thecowgoesmoo/TwinCl/CNC/files/octave_naturals_v2.png

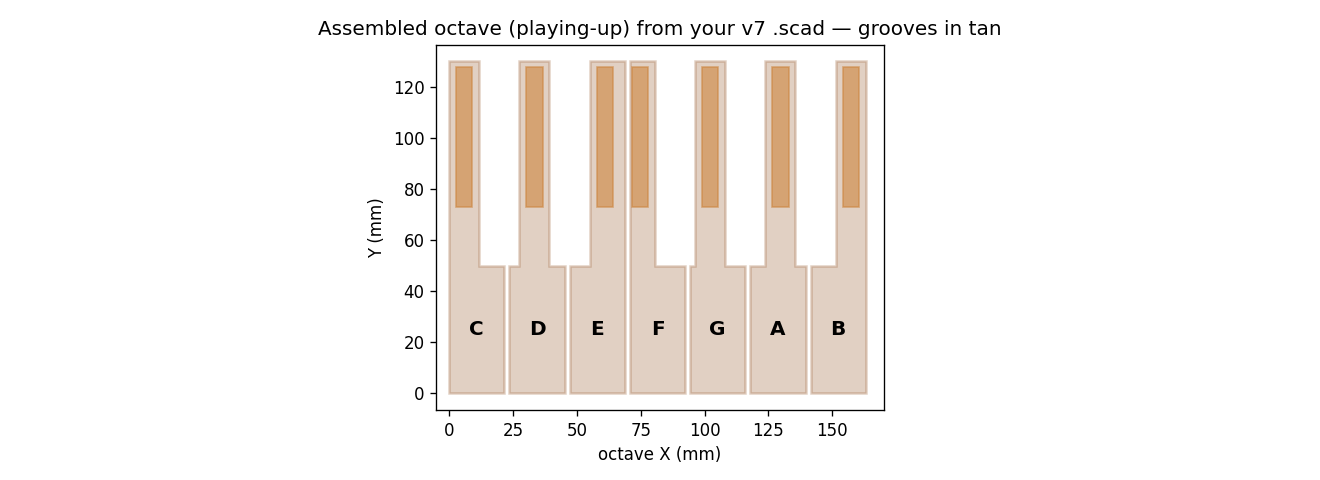
CNC/files/octave_naturals_v2.png
