thecowgoesmoo/TwinCl/model_sim/FirstPulse_simRigidExc.png

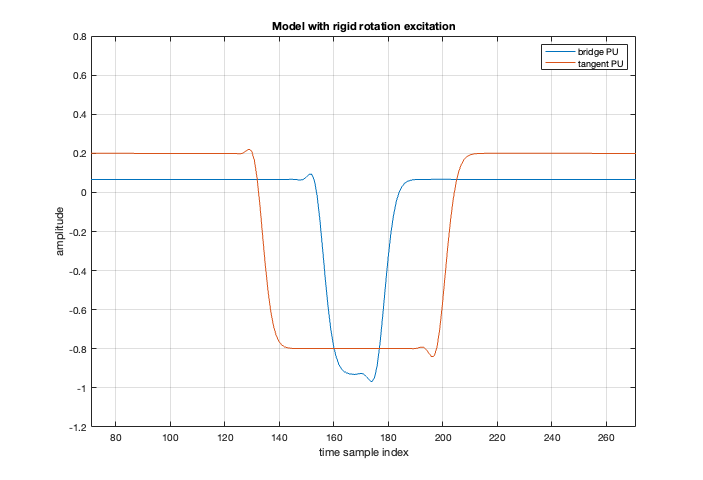
model_sim/FirstPulse_simRigidExc.png
