thecowgoesmoo/TwinCl/model_sim/FirstPulse_TC002meas.png

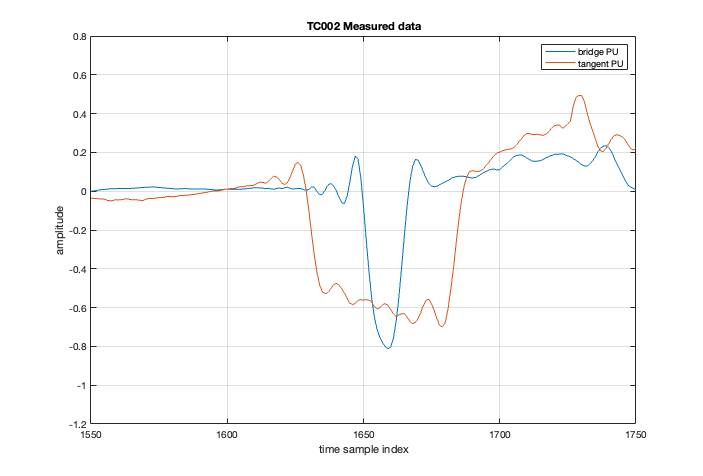
model_sim/FirstPulse_TC002meas.png
