thecowgoesmoo/TwinCl/model_sim/fitHCTparams_demo_hct.png

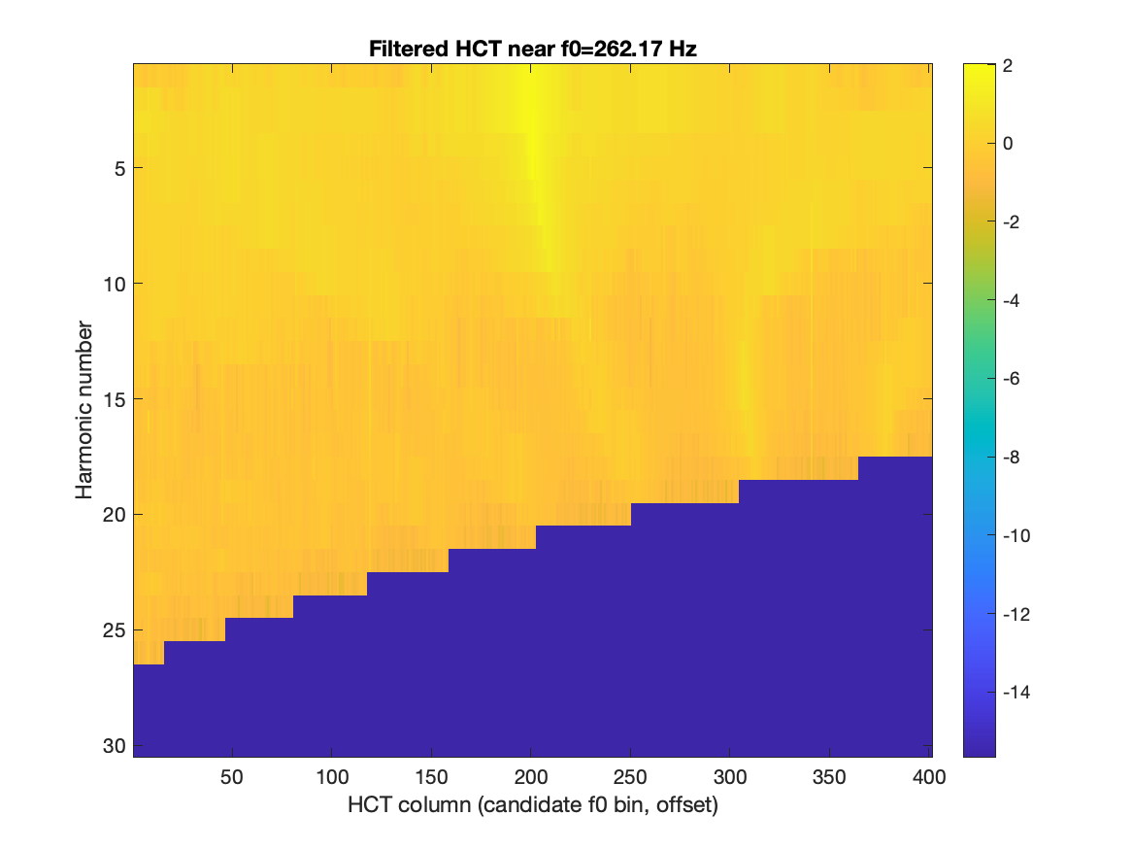
model_sim/fitHCTparams_demo_hct.png
