thecowgoesmoo/TwinCl/model_sim/fitHCTparams_demo_profile.png

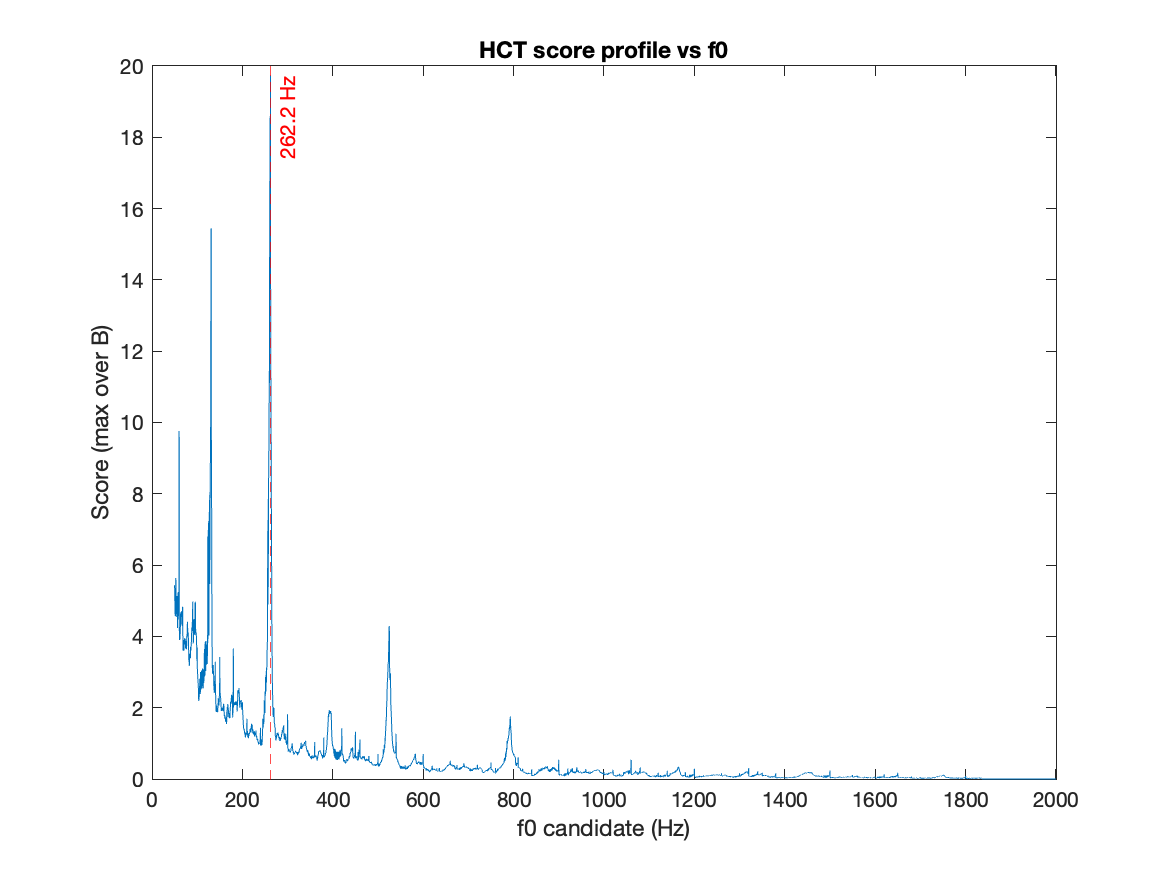
model_sim/fitHCTparams_demo_profile.png
