thecowgoesmoo/TwinCl/model_sim/fitHCTparams_demo_score.png

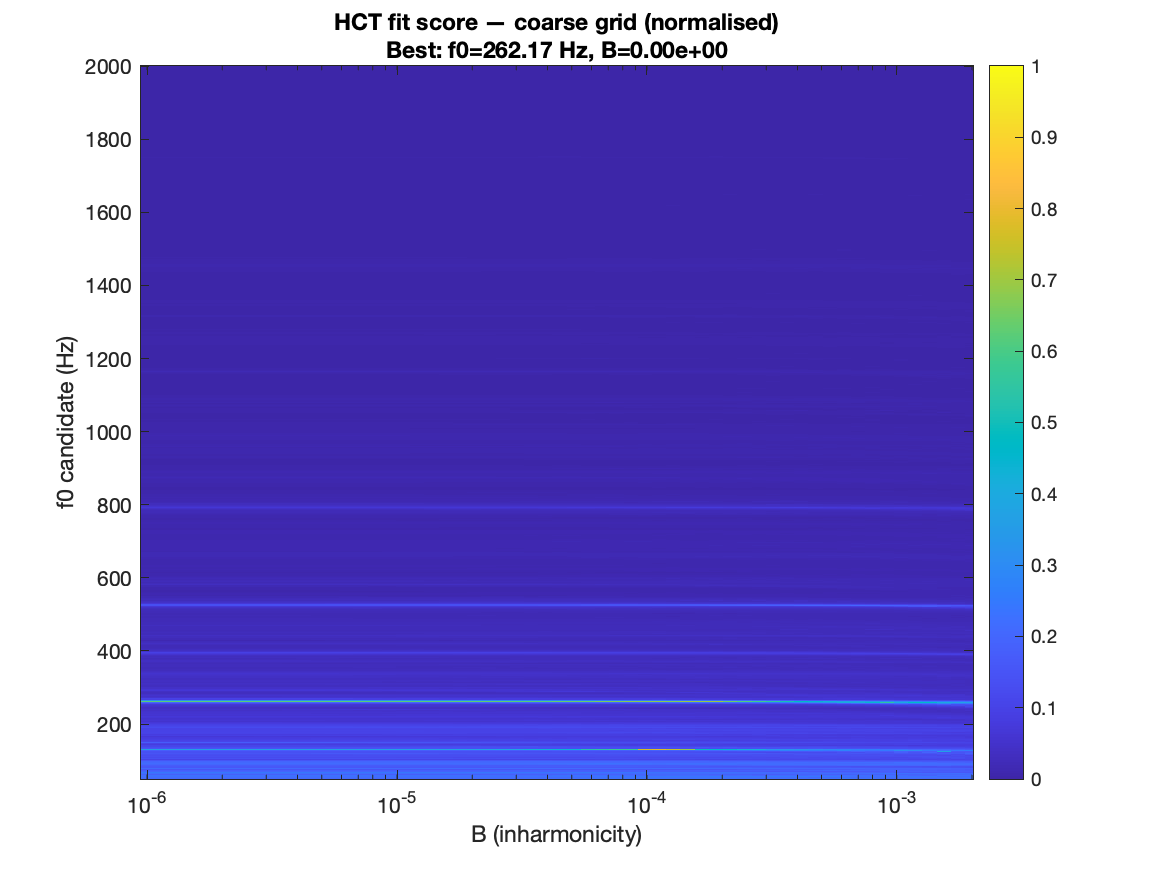
model_sim/fitHCTparams_demo_score.png
