thecowgoesmoo/TwinCl/prototypes/TC-001/media/photos/TwinCl_v1.jpeg

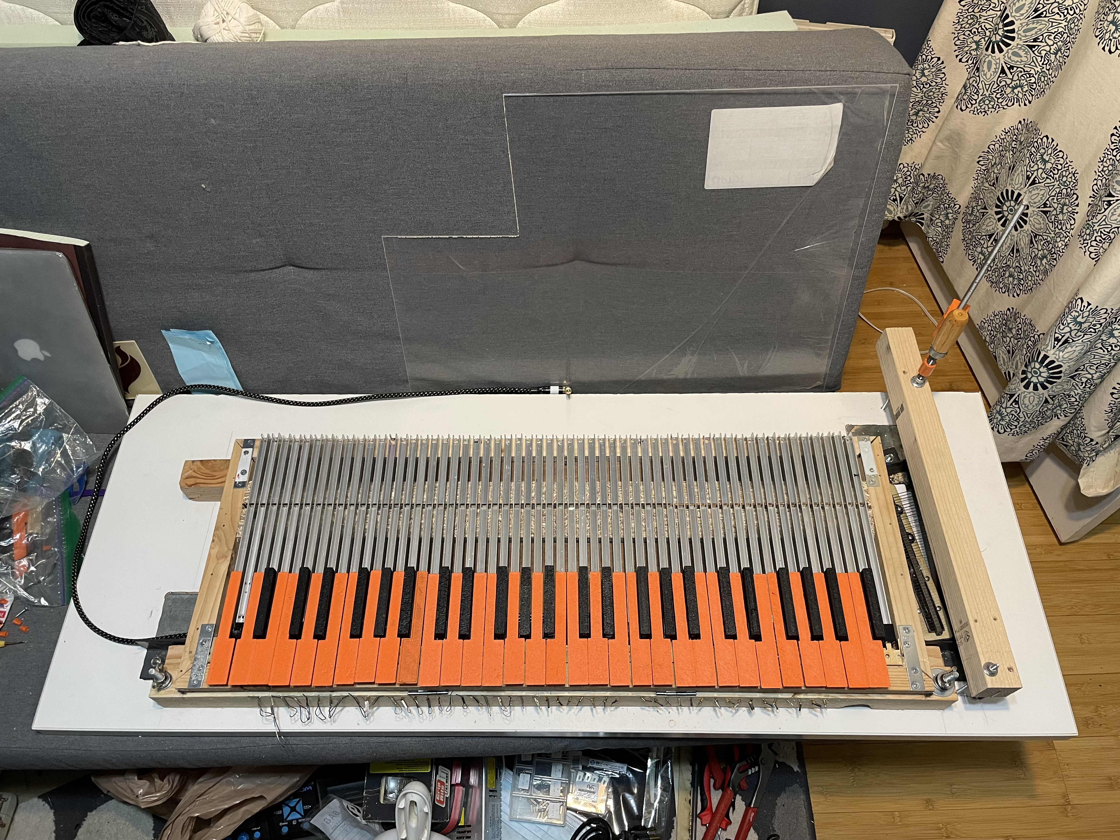
prototypes/TC-001/media/photos/TwinCl_v1.jpeg
