thecowgoesmoo/TwinCl/prototypes/TC-001/media/photos/TwinCl_v1_open.jpeg

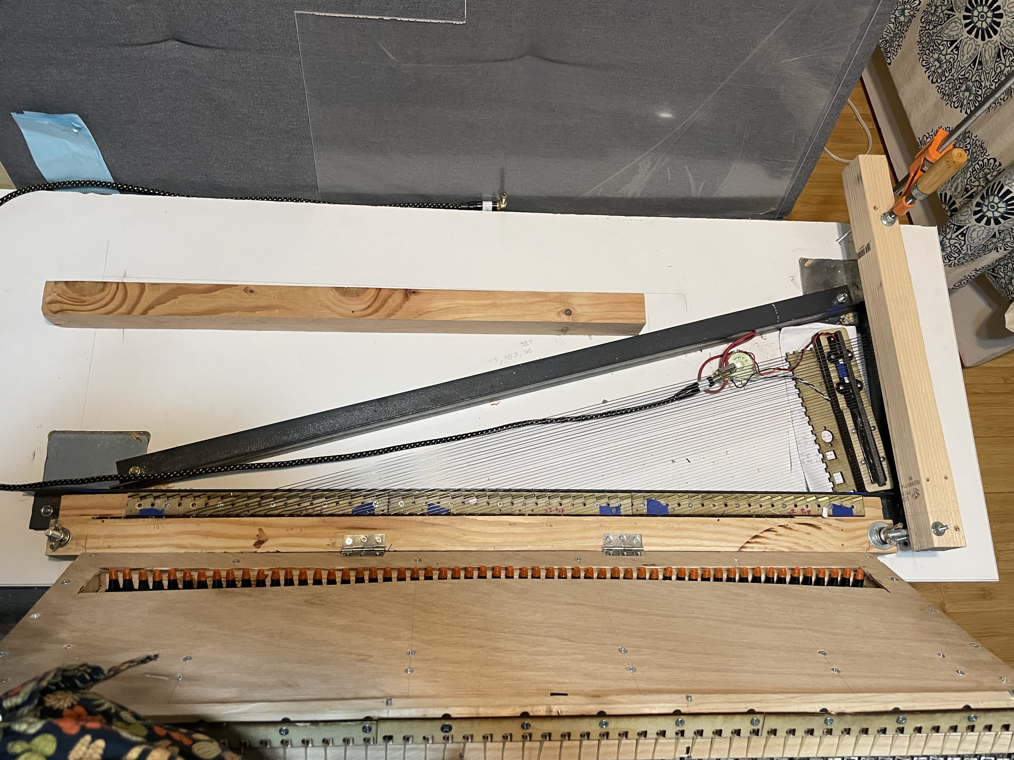
prototypes/TC-001/media/photos/TwinCl_v1_open.jpeg
