thecowgoesmoo/TwinCl/prototypes/TC-002/media/photos/HarpV2.jpeg

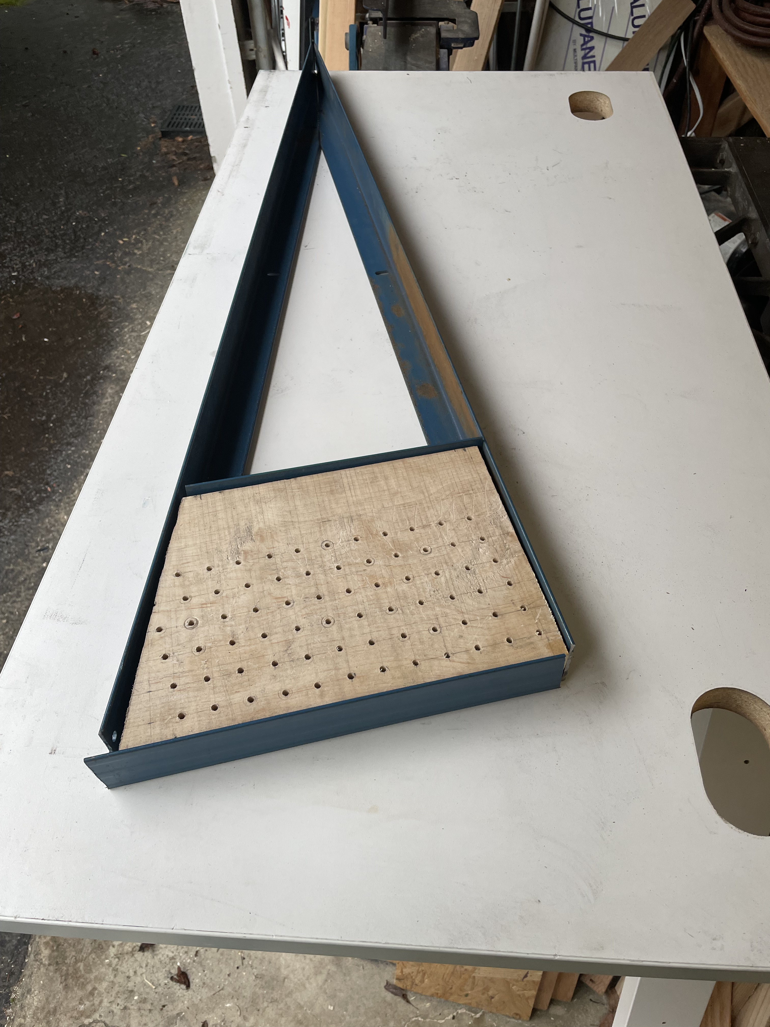
prototypes/TC-002/media/photos/HarpV2.jpeg
