thecowgoesmoo/TwinCl/prototypes/TC-002/media/photos/SupahTunah.jpeg

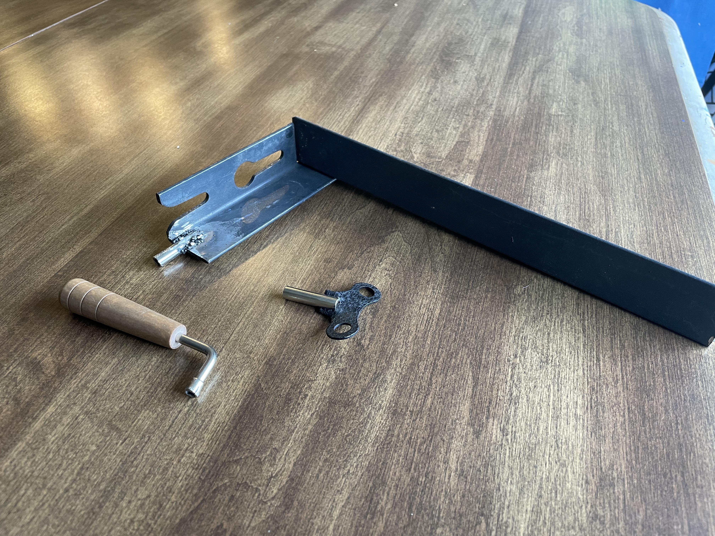
prototypes/TC-002/media/photos/SupahTunah.jpeg
