thecowgoesmoo/TwinCl/prototypes/TC-002/media/photos/TwinCl_v2_KeyworkDetail.jpeg

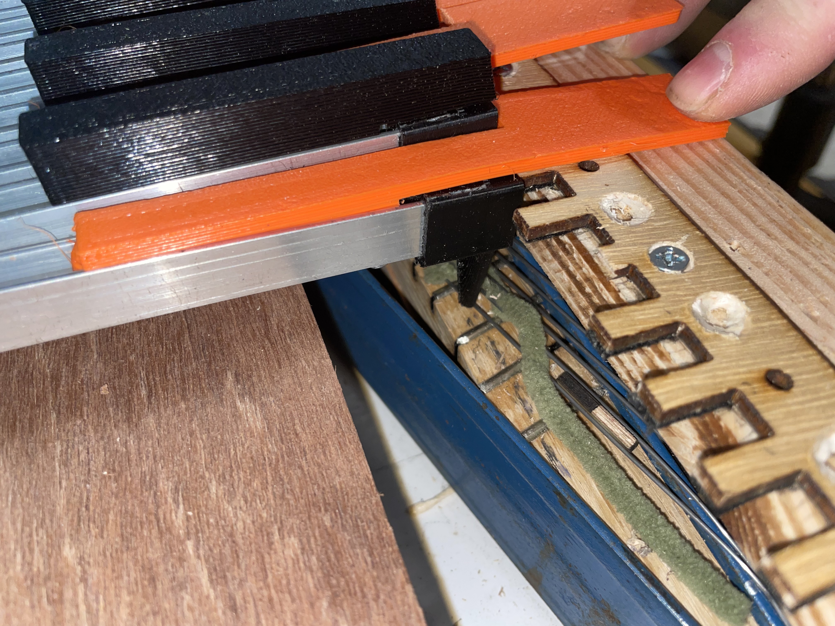
prototypes/TC-002/media/photos/TwinCl_v2_KeyworkDetail.jpeg
