thecowgoesmoo/TwinCl/prototypes/TC-003/media/photos/IMG_6832.jpeg

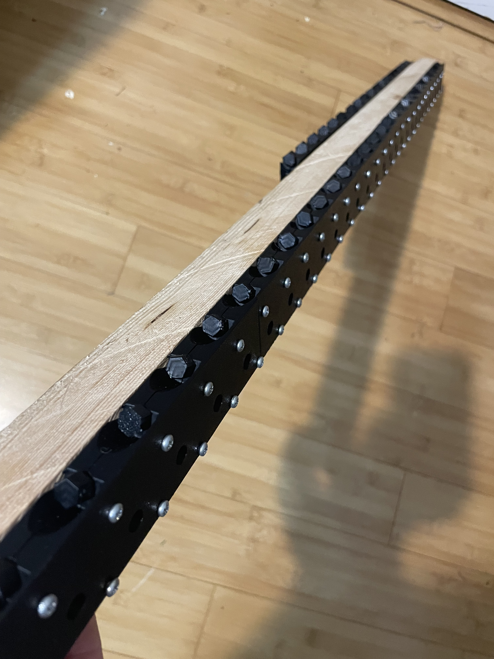
prototypes/TC-003/media/photos/IMG_6832.jpeg
