thecowgoesmoo/TwinCl/prototypes/TC-003/media/photos/IMG_6854.jpeg

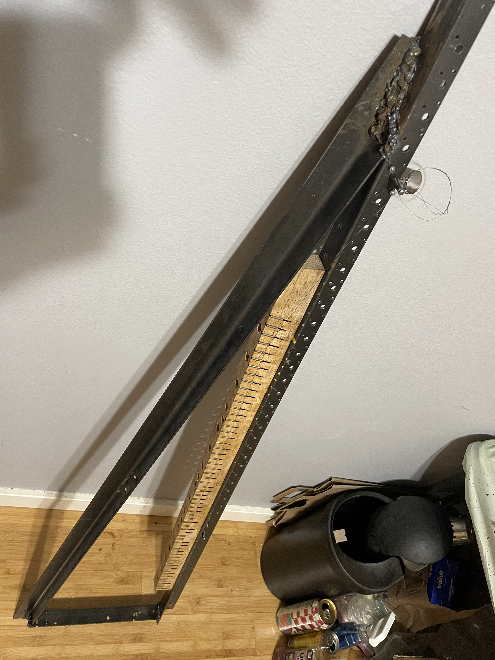
prototypes/TC-003/media/photos/IMG_6854.jpeg
