thecowgoesmoo/TwinCl/prototypes/TC-003/media/photos/IMG_6858.jpeg

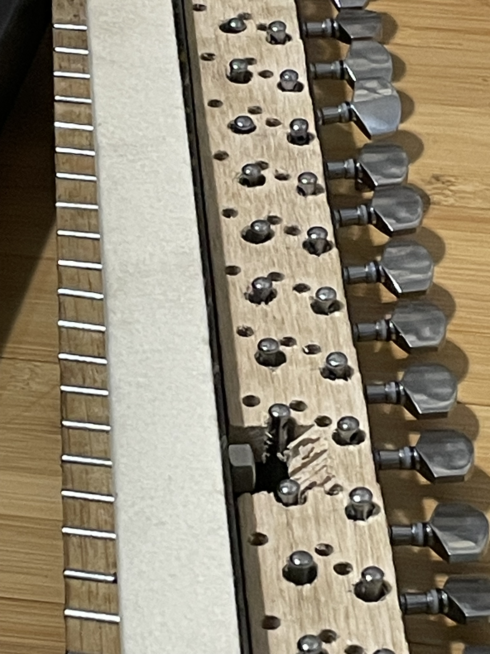
prototypes/TC-003/media/photos/IMG_6858.jpeg
