thecowgoesmoo/TwinCl/prototypes/TC-003/media/photos/IMG_6859.jpeg

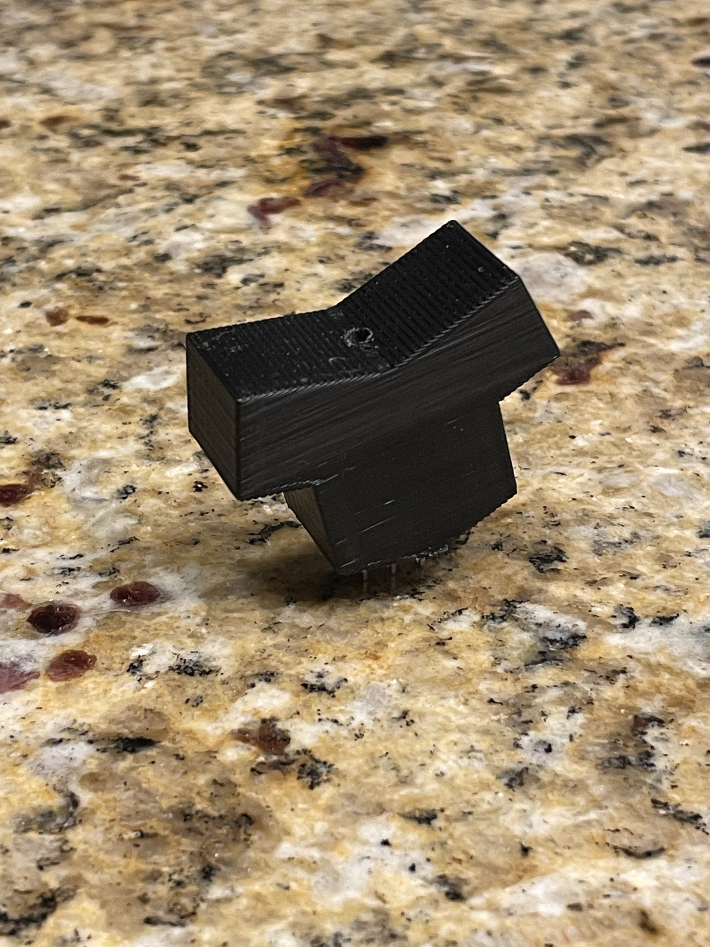
prototypes/TC-003/media/photos/IMG_6859.jpeg
