thecowgoesmoo/TwinCl/prototypes/TC-003/media/photos/IMG_6860.jpeg

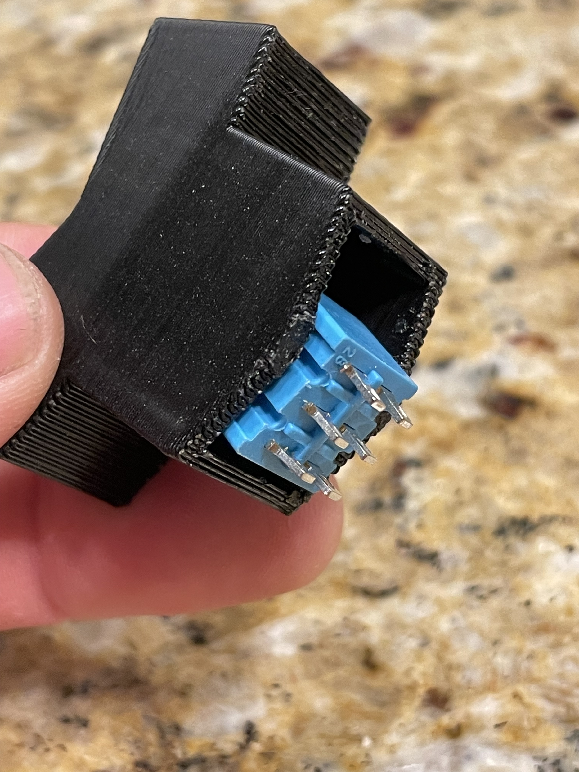
prototypes/TC-003/media/photos/IMG_6860.jpeg
