thecowgoesmoo/TwinCl/print_files/irkem_TwinCl_SwitchRockerABv3.stl

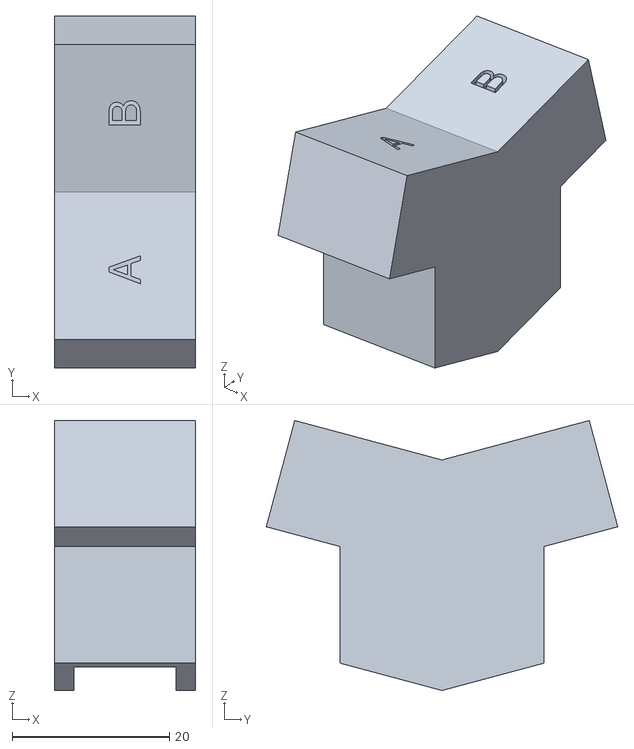
[picture p50: CAD file, 2026-04-17]
print_files/irkem_TwinCl_SwitchRockerABv3.stl
18.0 x 44.7 x 34.4
