thecowgoesmoo/TwinCl/print_files/irkem_TwinCl_SwitchRocker_BRILLIANT.stl

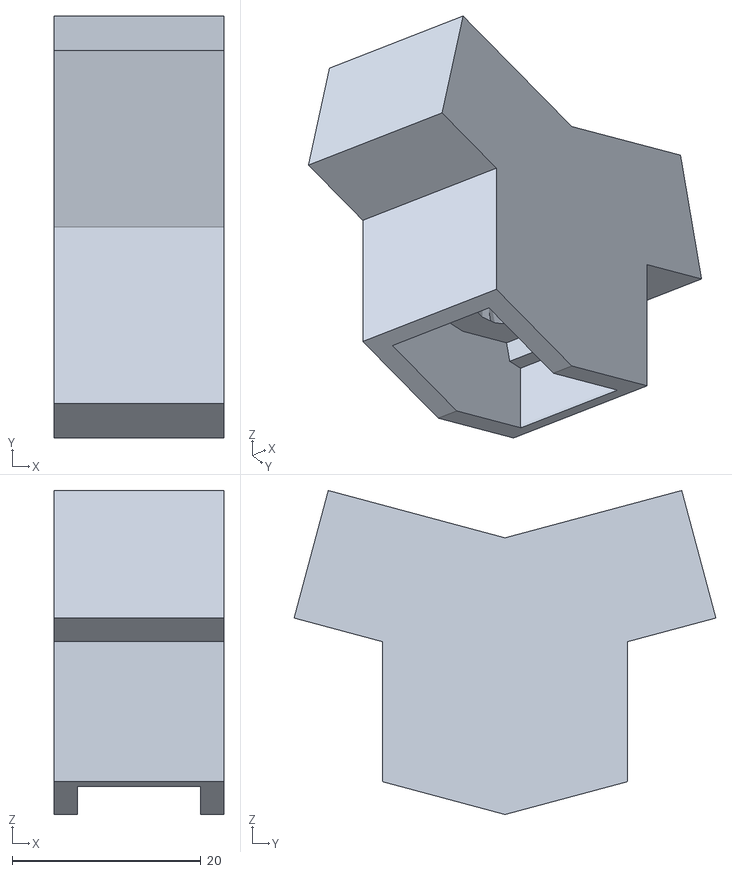
[picture p51: CAD file, 2026-04-17]
print_files/irkem_TwinCl_SwitchRocker_BRILLIANT.stl
18.0 x 44.7 x 34.4
