thecowgoesmoo/TwinCl/print_files/irkem_TwinCl_SwitchRocker_BRILLIANTv2.stl

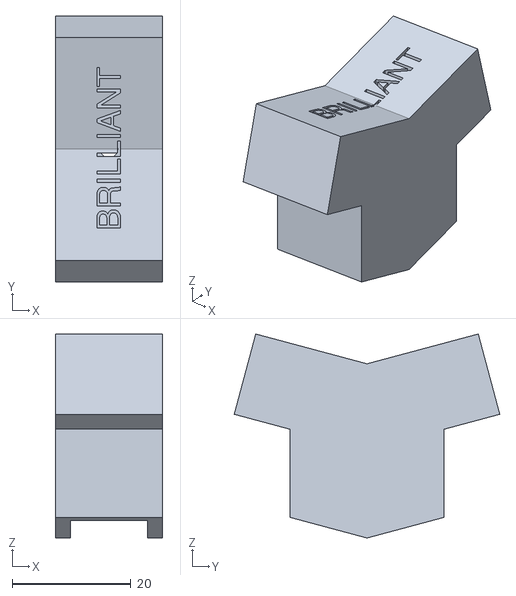
[picture p52: CAD file, 2026-04-17]
print_files/irkem_TwinCl_SwitchRocker_BRILLIANTv2.stl
18.0 x 44.7 x 34.4
