thecowgoesmoo/TwinCl/print_files/irkem_TwHxWrmV3.stl

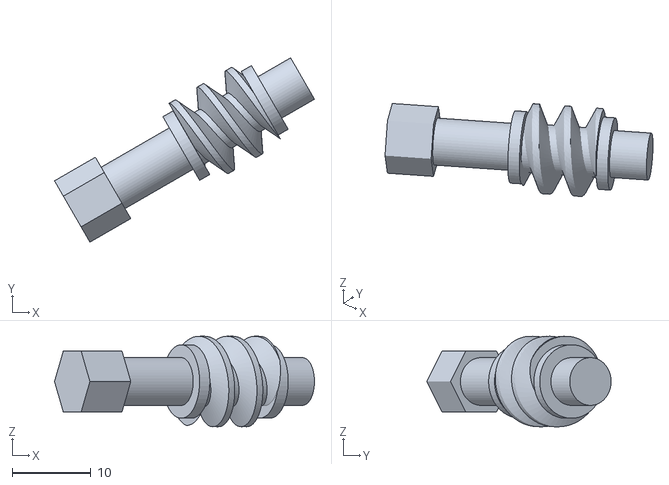
[picture p53: CAD file, 2026-04-04]
print_files/irkem_TwHxWrmV3.stl
33.0 x 23.4 x 11.5
