thecowgoesmoo/TwinCl/print_files/irkem_TwinCl_wormGearV2.stl

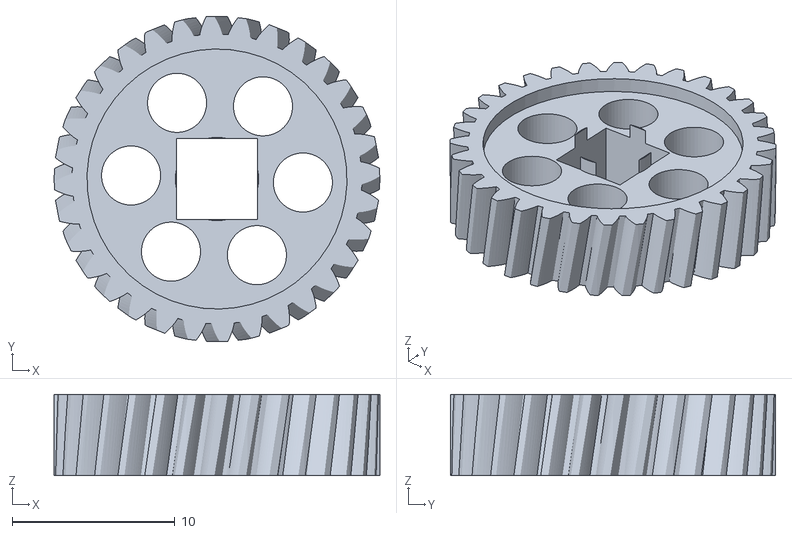
[picture p54: CAD file, 2026-04-04]
print_files/irkem_TwinCl_wormGearV2.stl
20.0 x 20.0 x 5.00
