thecowgoesmoo/TwinCl/print_files/irkem_TwHxSprV3.stl

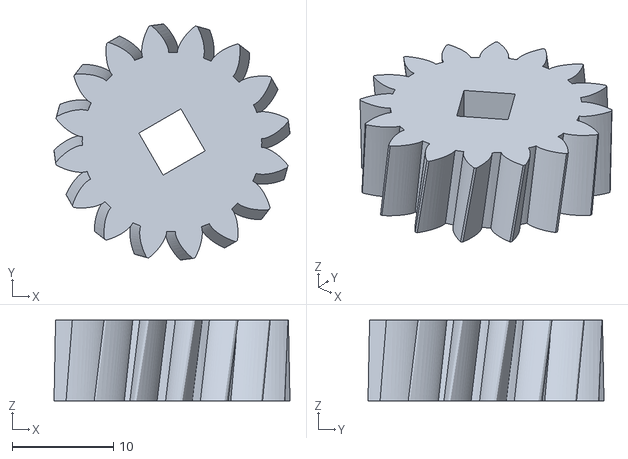
[picture p55: CAD file, 2026-04-04]
print_files/irkem_TwHxSprV3.stl
23.3 x 23.3 x 8.00
