thecowgoesmoo/TwinCl/print_files/irkem_TPUtip_v2.stl

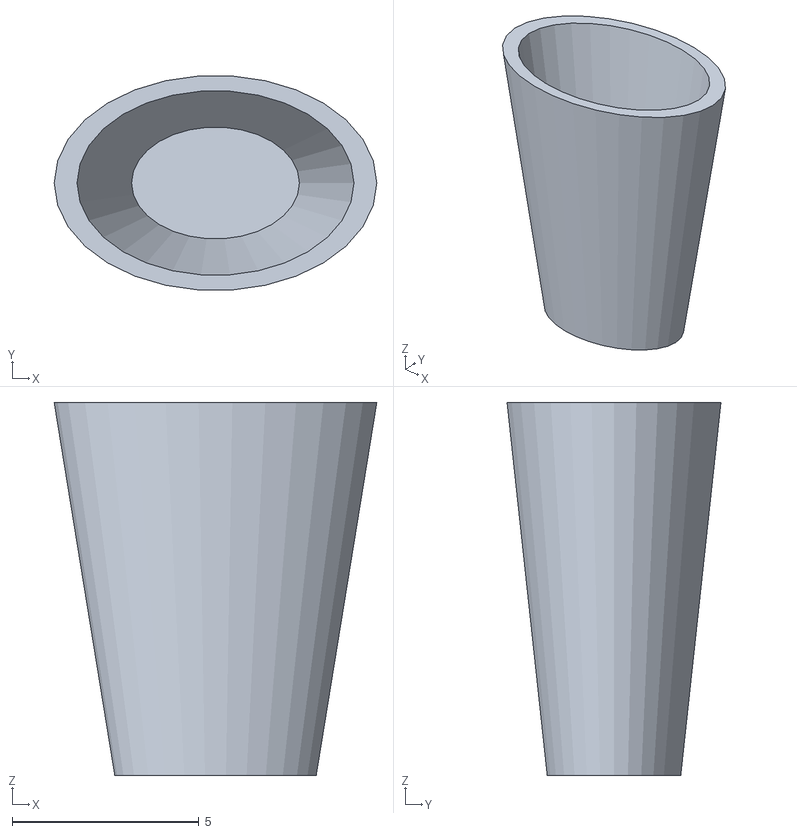
[picture p56: CAD file, 2026-03-12]
print_files/irkem_TPUtip_v2.stl
8.65 x 5.74 x 10.0
