thecowgoesmoo/TwinCl/print_files/irkem_PrStrGd_v2.stl

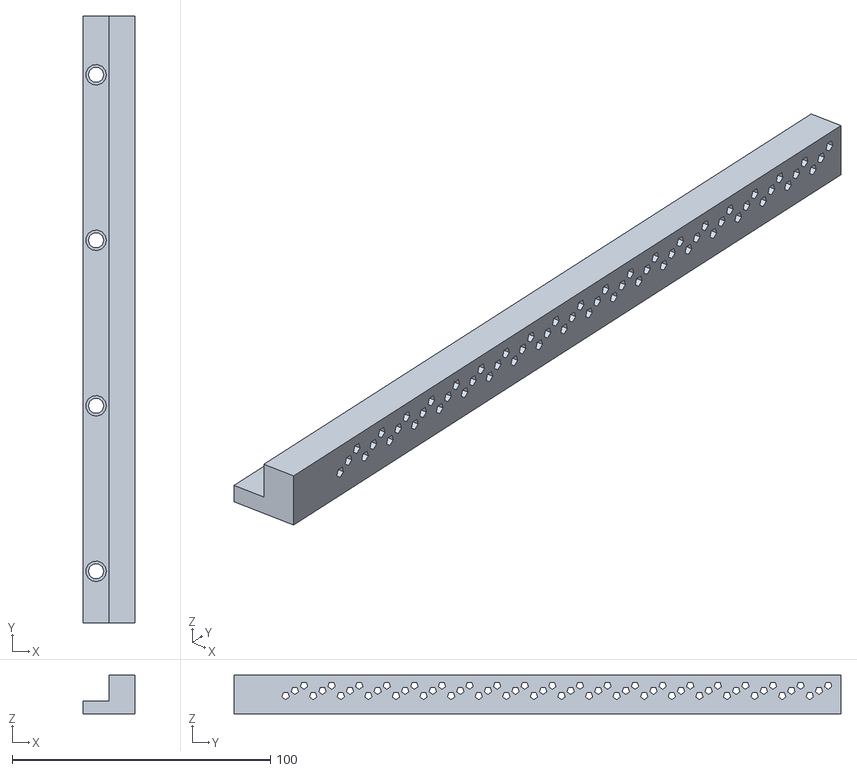
[picture p57: CAD file, 2026-03-12]
print_files/irkem_PrStrGd_v2.stl
20.0 x 235.0 x 15.0
