thecowgoesmoo/TwinCl/print_files/irkem_PrStrEndBlck_v0.stl

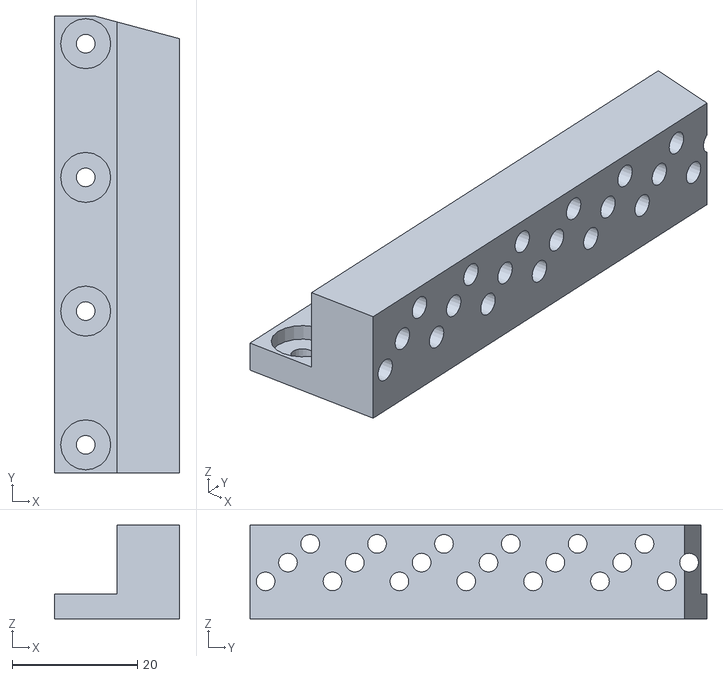
[picture p58: CAD file, 2026-03-12]
print_files/irkem_PrStrEndBlck_v0.stl
20.0 x 73.0 x 15.0
