thecowgoesmoo/TwinCl/print_files/irkem_Pickup_v0.stl

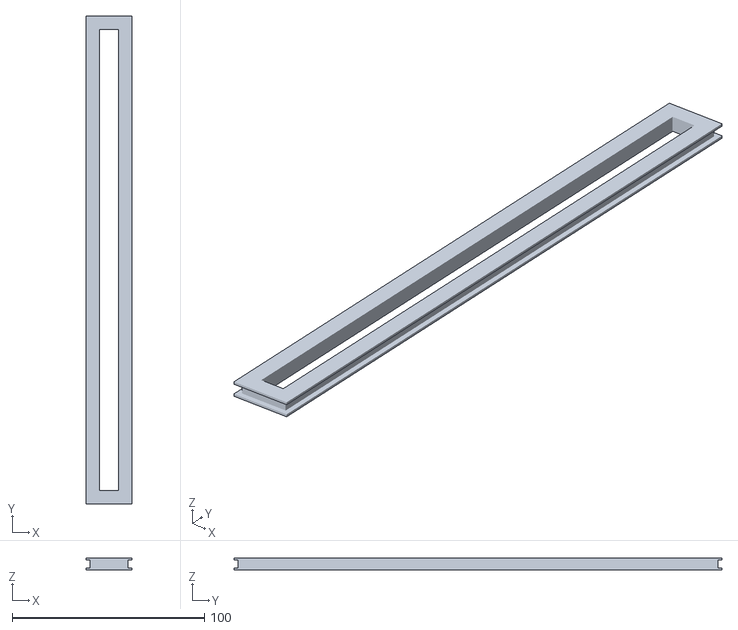
[picture p59: CAD file, 2026-03-12]
print_files/irkem_Pickup_v0.stl
24.0 x 254.0 x 6.00
