thecowgoesmoo/TwinCl/print_files/irkem_keycaps_v3.stl

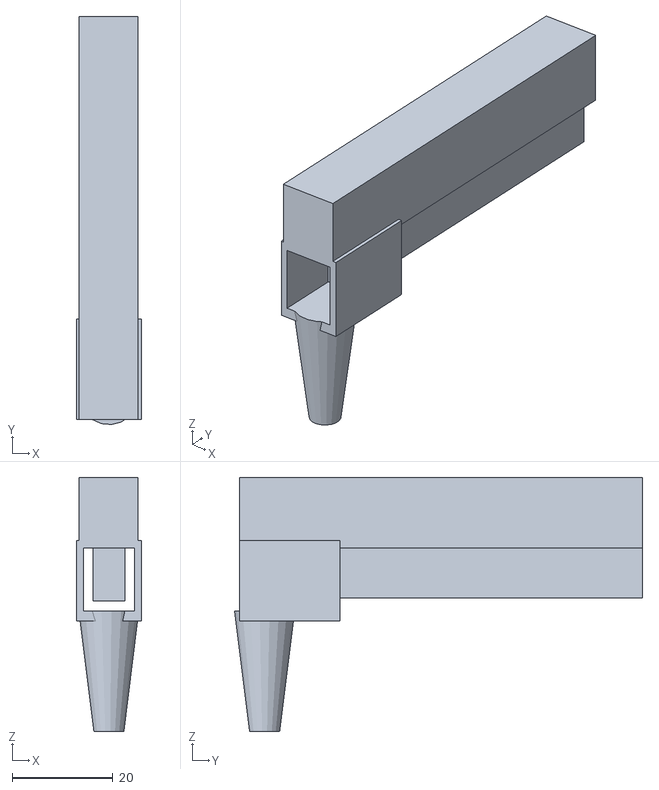
[picture p60: CAD file, 2026-02-07]
print_files/irkem_keycaps_v3.stl
13.0 x 81.0 x 50.5
