thecowgoesmoo/TwinCl/print_files/irkem_accKeycap_v3.stl

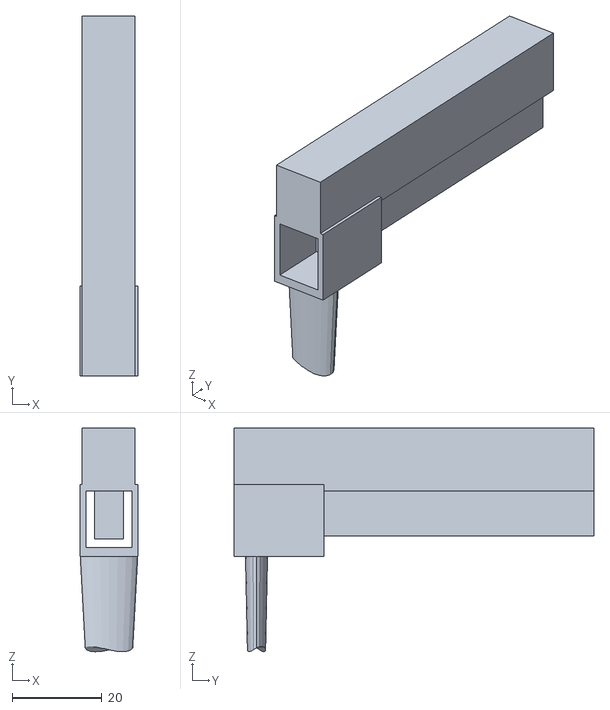
[picture p61: CAD file, 2026-02-07]
print_files/irkem_accKeycap_v3.stl
13.0 x 80.0 x 49.7
