thecowgoesmoo/TwinCl/print_files/irkem_natkeycaps_v1.stl

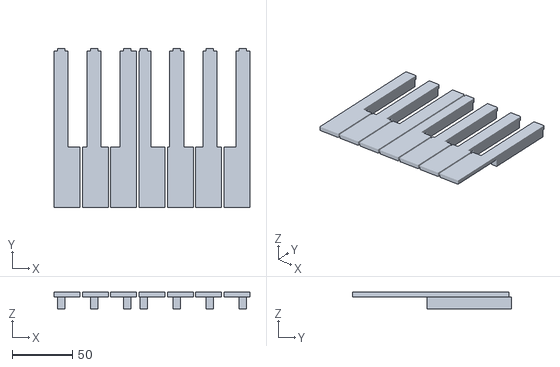
[picture p62: CAD file, 2026-01-31]
print_files/irkem_natkeycaps_v1.stl
163.1 x 132.0 x 14.0
