thecowgoesmoo/TwinCl/print_files/irkem_sharpKeycaps_v0.stl

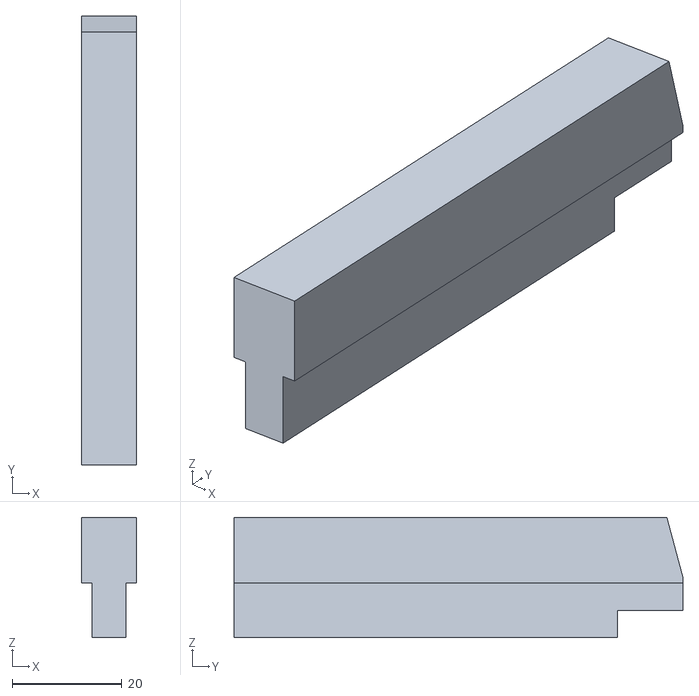
[picture p63: CAD file, 2026-01-31]
print_files/irkem_sharpKeycaps_v0.stl
10.0 x 82.0 x 22.0
