thecowgoesmoo/TwinCl/CAD/irkem_notATunah_v0.scad

translate([0,0,0]) cube([30,30,30]);
