thecowgoesmoo/TwinCl/prototypes/TC-001/media/measurements/key_return_time_ms.csv

# Requirement: keys return within 100 ms of release
# Method: TODO (e.g. high-speed video or contact switch timing)
key_number,key_note,return_time_ms,notes
# TODO: 60 rows, one per key
