thecowgoesmoo/TwinCl/prototypes/TC-001/media/measurements/keywork_noise_dBA.csv

# Requirement: keywork makes less than 50 dBA during play (excluding string noise)
# Method: TODO (e.g. calibrated microphone at 1m, damped strings, playing at normal velocity)
measurement_id,condition,distance_m,level_dBA,notes
