thecowgoesmoo/TwinCl/prototypes/TC-001/media/photos/harp_stringing.jpeg

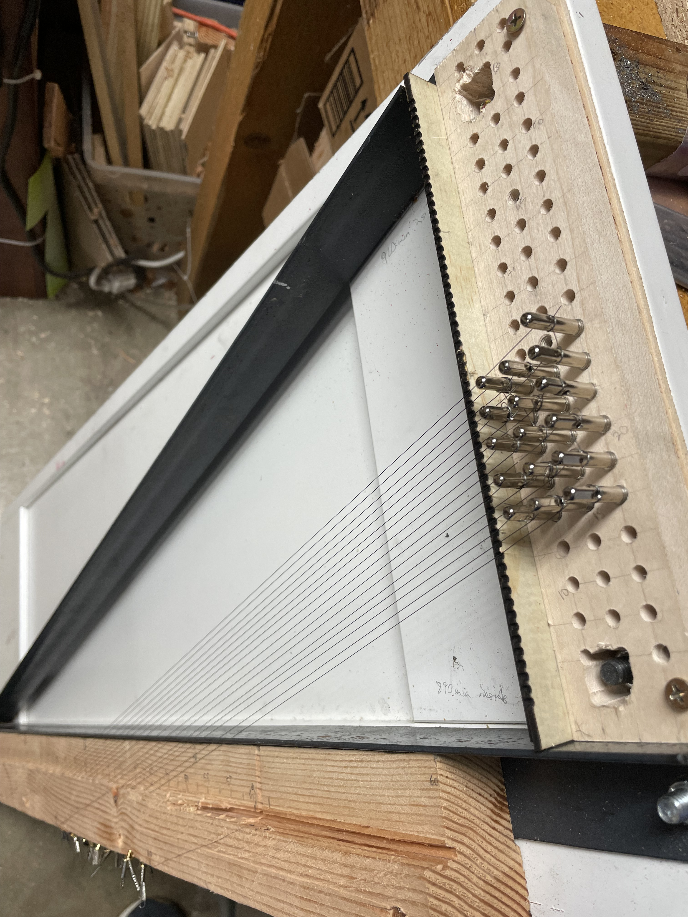
prototypes/TC-001/media/photos/harp_stringing.jpeg
