thecowgoesmoo/TwinCl/prototypes/TC-001/media/photos/HarpV2_weldDetail.jpeg

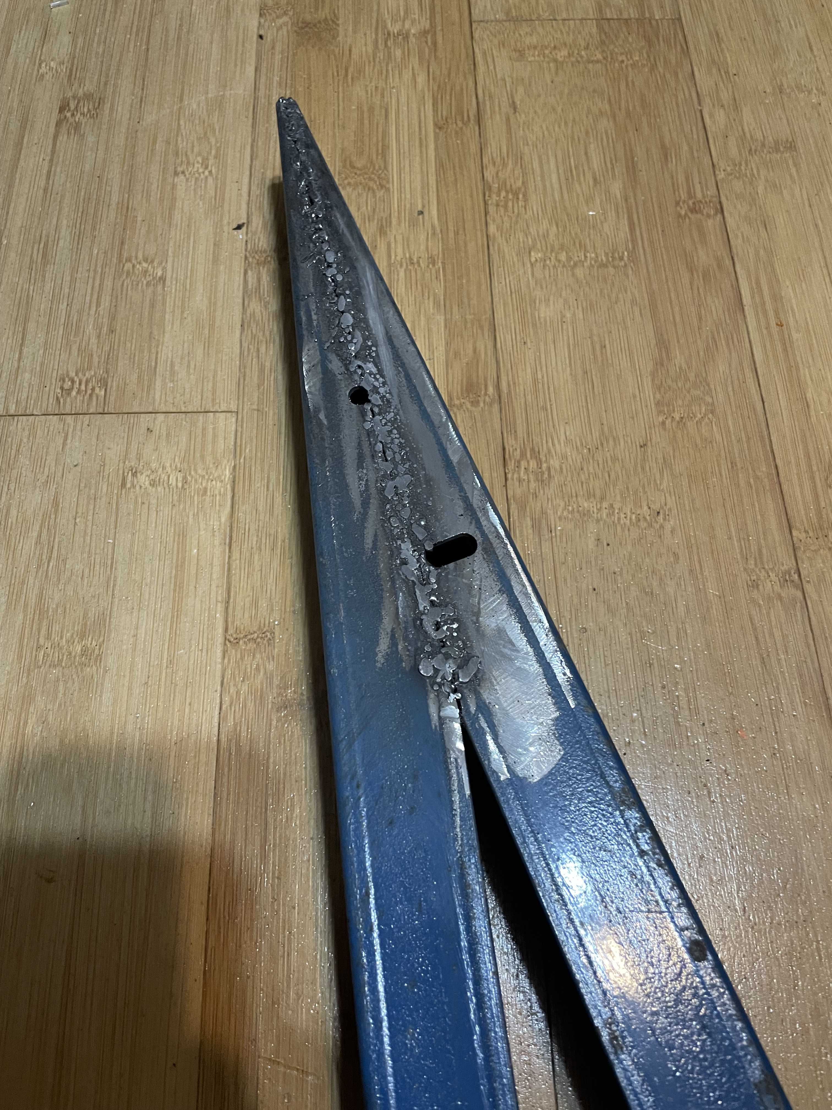
prototypes/TC-001/media/photos/HarpV2_weldDetail.jpeg
