thecowgoesmoo/TwinCl/prototypes/TC-001/media/photos/keybed_to_harp_alignment.jpeg

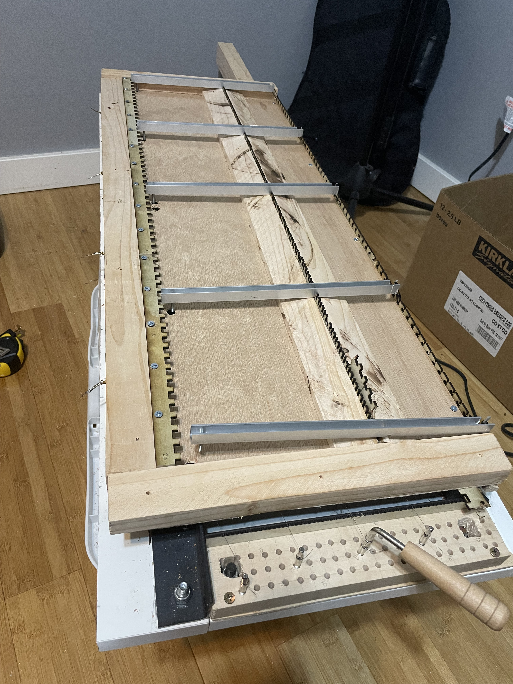
prototypes/TC-001/media/photos/keybed_to_harp_alignment.jpeg
