thecowgoesmoo/TwinCl/prototypes/TC-002/media/photos/TwinCl_v2_leftSide.jpeg

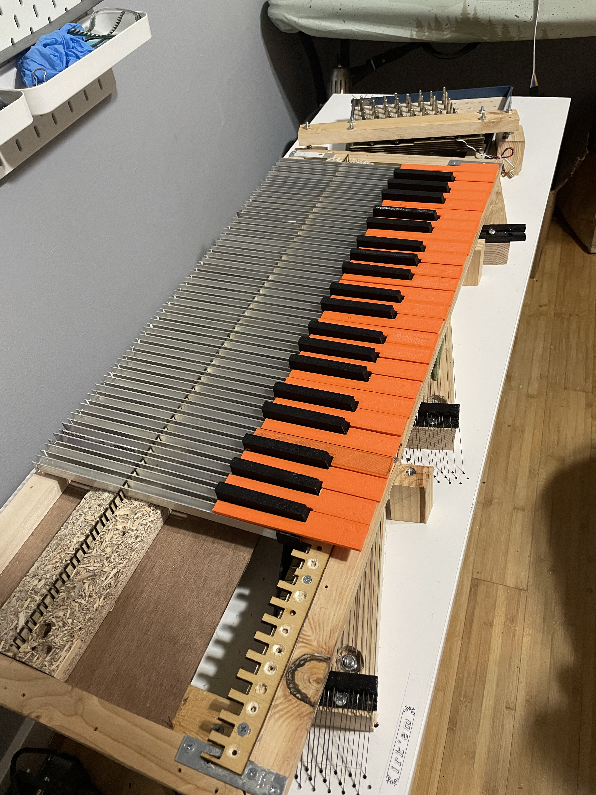
prototypes/TC-002/media/photos/TwinCl_v2_leftSide.jpeg
