thecowgoesmoo/TwinCl/prototypes/TC-003/media/photos/IMG_6834.jpeg

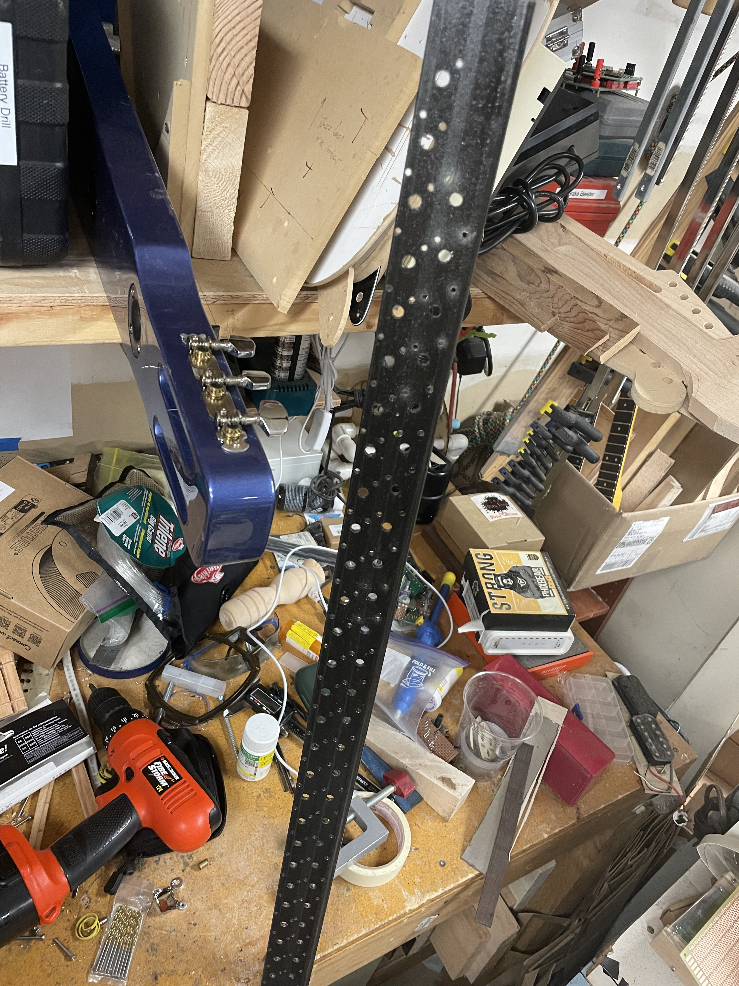
prototypes/TC-003/media/photos/IMG_6834.jpeg
