thecowgoesmoo/TwinCl/prototypes/TC-003/media/photos/IMG_6835.jpeg

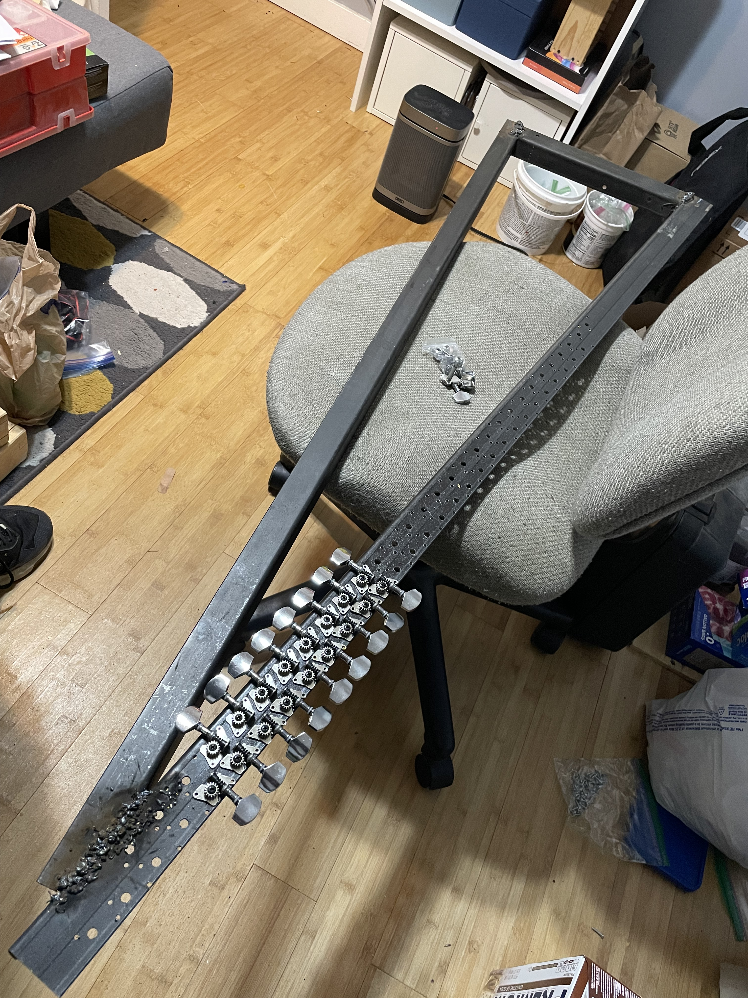
prototypes/TC-003/media/photos/IMG_6835.jpeg
