thecowgoesmoo/TwinCl/prototypes/TC-003/media/photos/IMG_6837.jpeg

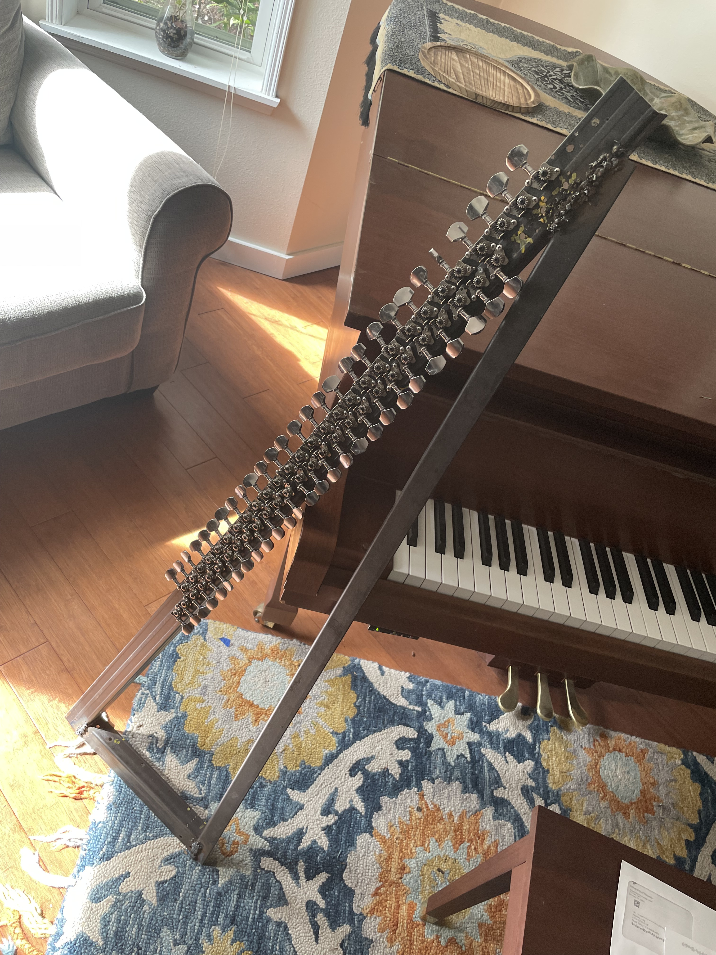
prototypes/TC-003/media/photos/IMG_6837.jpeg
