thecowgoesmoo/TwinCl/prototypes/TC-003/media/photos/IMG_6842.jpeg

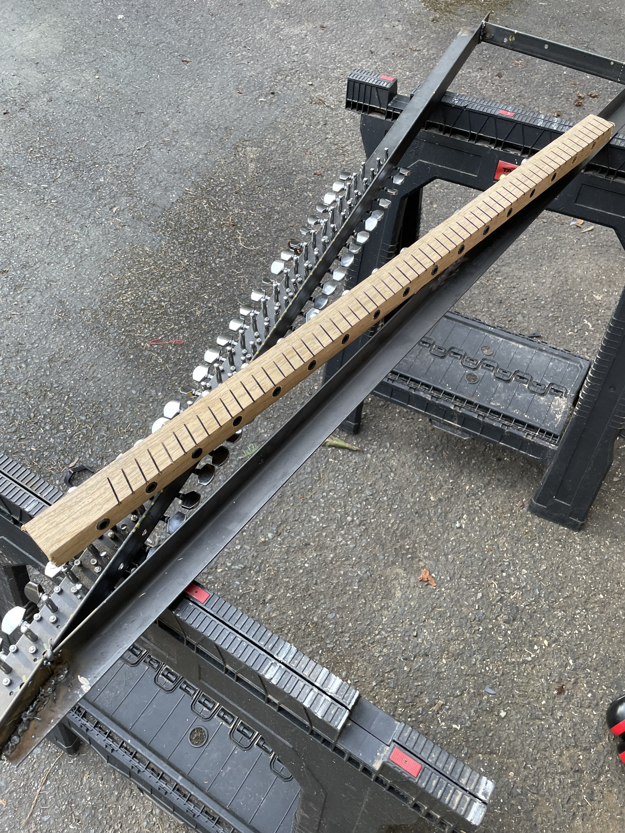
prototypes/TC-003/media/photos/IMG_6842.jpeg
