thecowgoesmoo/TwinCl/prototypes/TC-003/media/photos/IMG_6846.jpeg

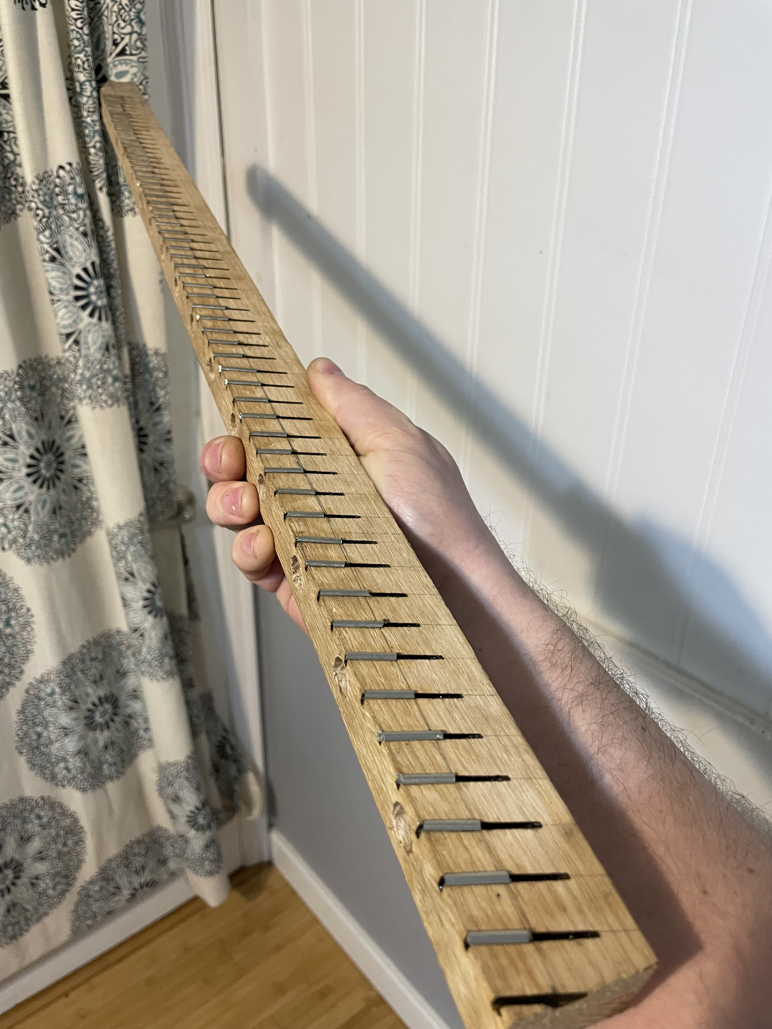
prototypes/TC-003/media/photos/IMG_6846.jpeg
