thecowgoesmoo/TwinCl/prototypes/TC-003/media/photos/IMG_6857.jpeg

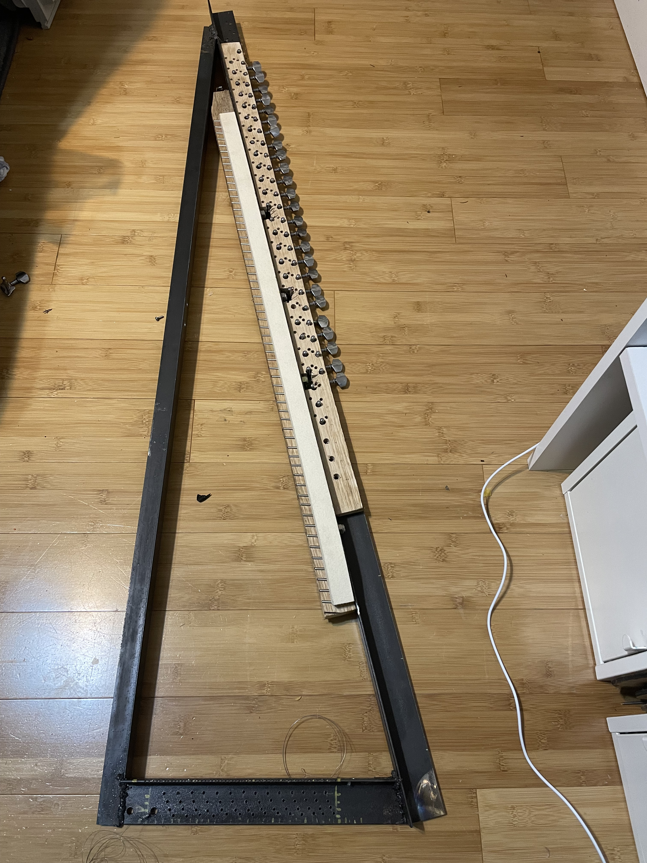
prototypes/TC-003/media/photos/IMG_6857.jpeg
