thecowgoesmoo/TwinCl/prototypes/TC-001/media/photos/early_acoustic_play_test.jpeg

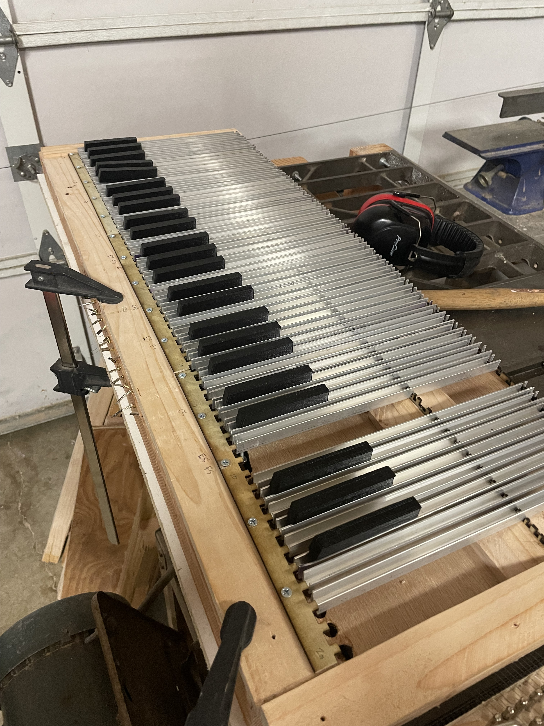
prototypes/TC-001/media/photos/early_acoustic_play_test.jpeg
